localdevices/libre360/images/IMG_1026.jpg

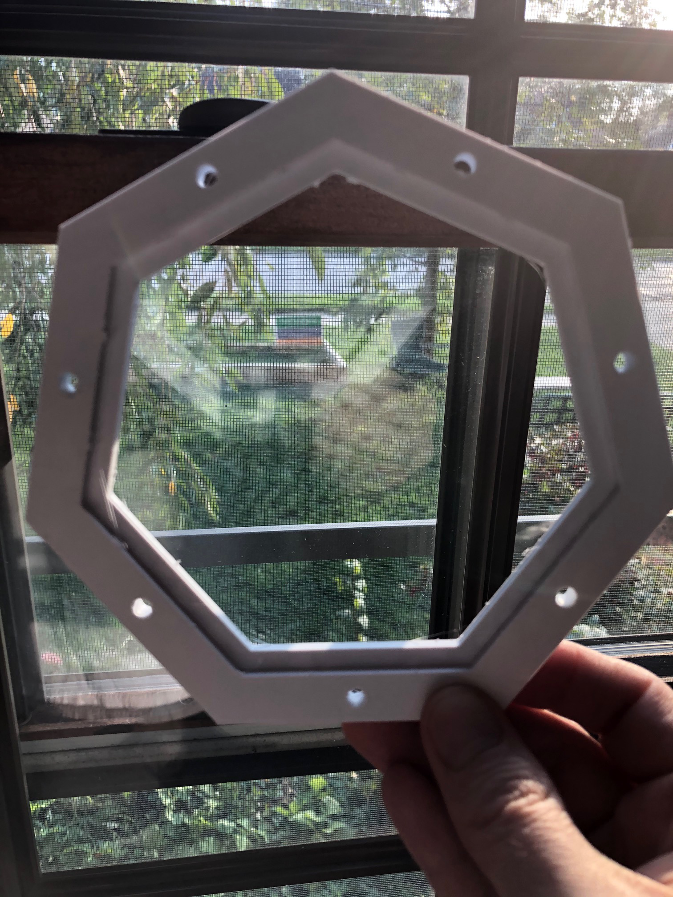
images/IMG_1026.jpg
