localdevices/libre360/images/IMG_1037.jpg

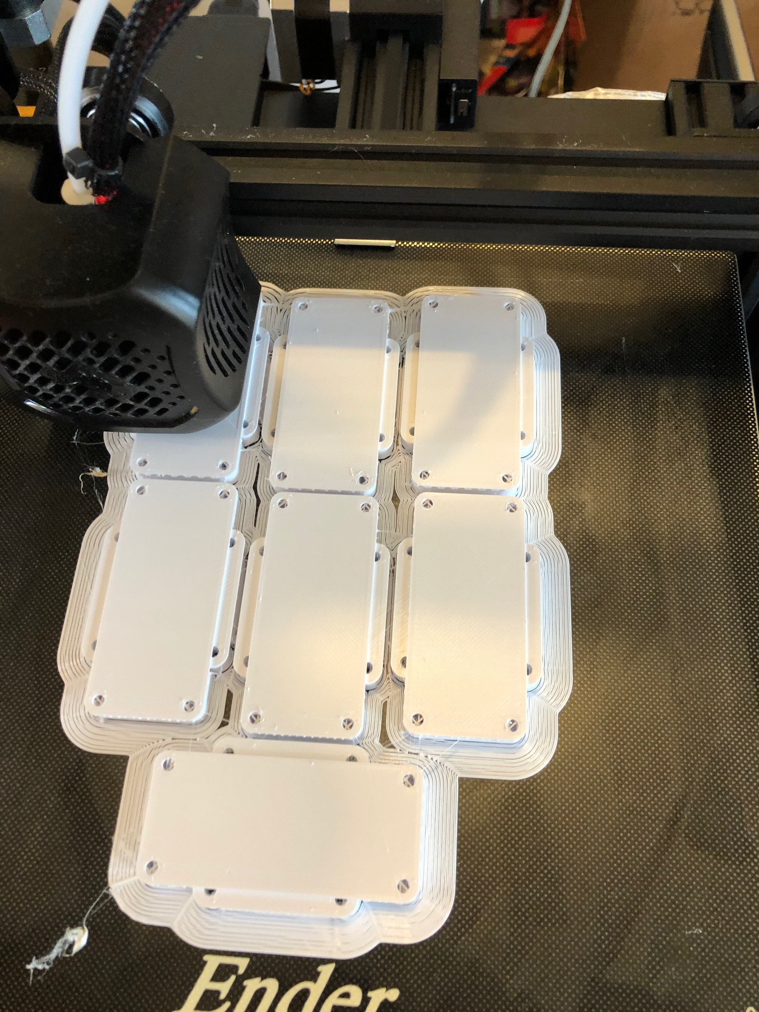
images/IMG_1037.jpg
